Dhugald/OP_ROVER/Photos/IMG_0927.JPG

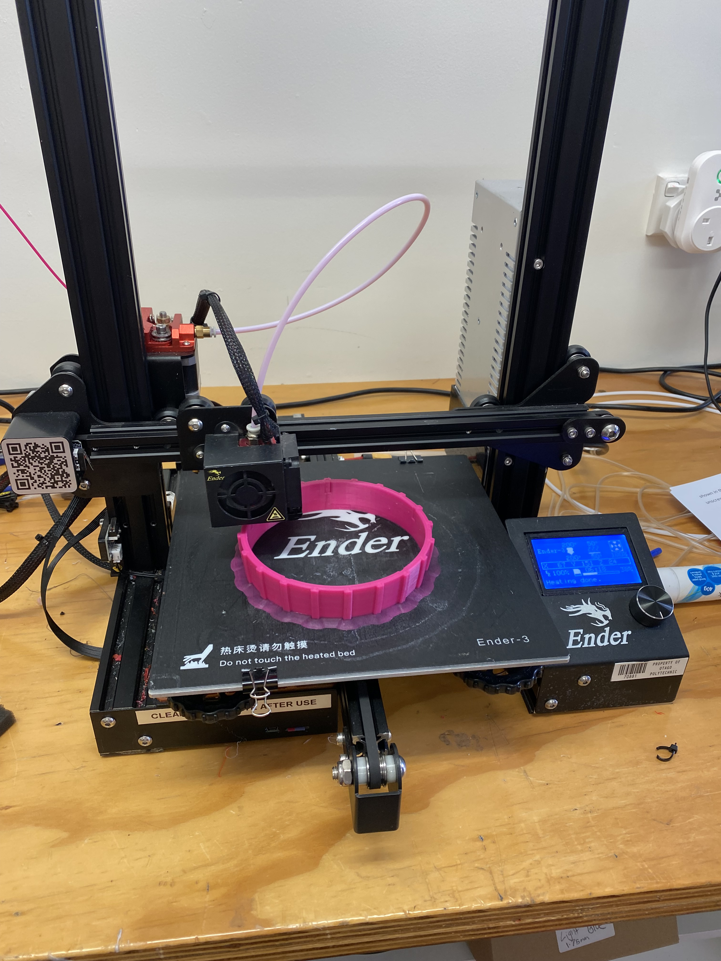
Photos/IMG_0927.JPG
