Dhugald/OP_ROVER/Photos/IMG_0928.JPG

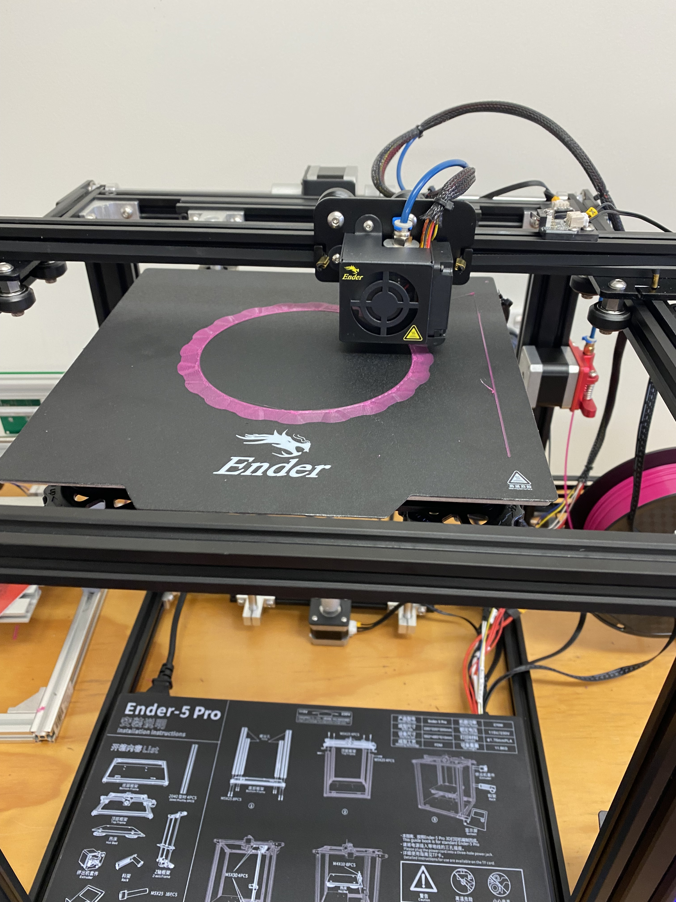
Photos/IMG_0928.JPG
