Dhugald/OP_ROVER/Photos/IMG_0930.JPG

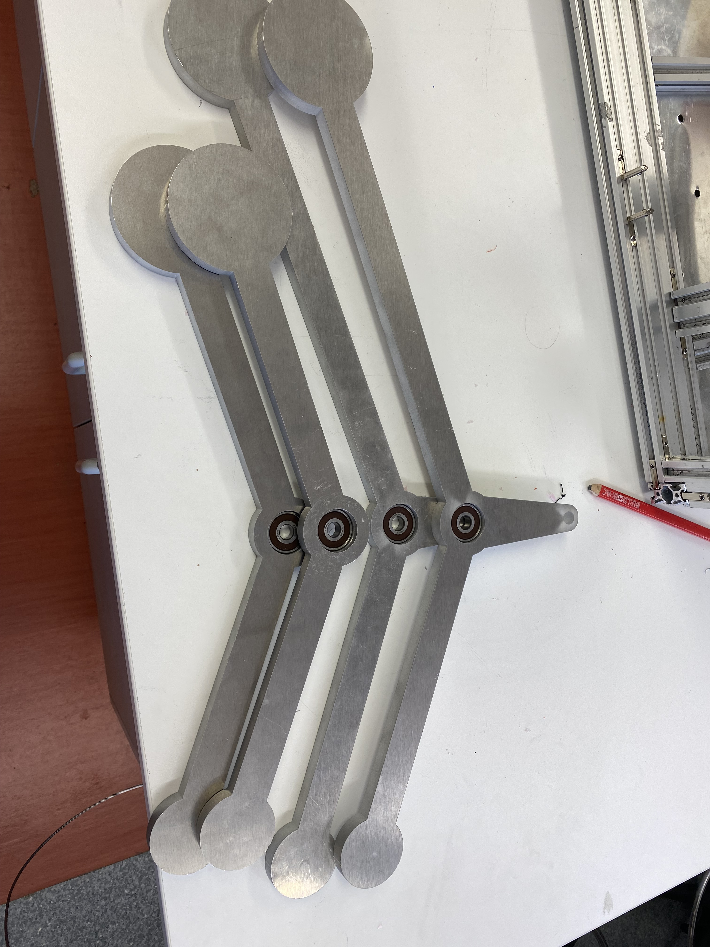
Photos/IMG_0930.JPG
