Dhugald/OP_ROVER/Photos/IMG_0931.JPG

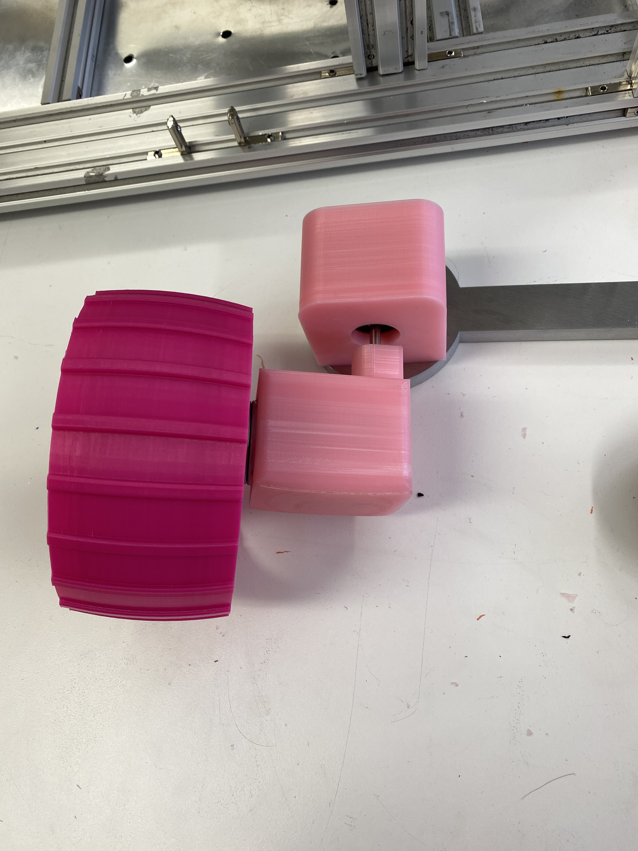
Photos/IMG_0931.JPG
