Dhugald/OP_ROVER/Photos/IMG_0986.JPG

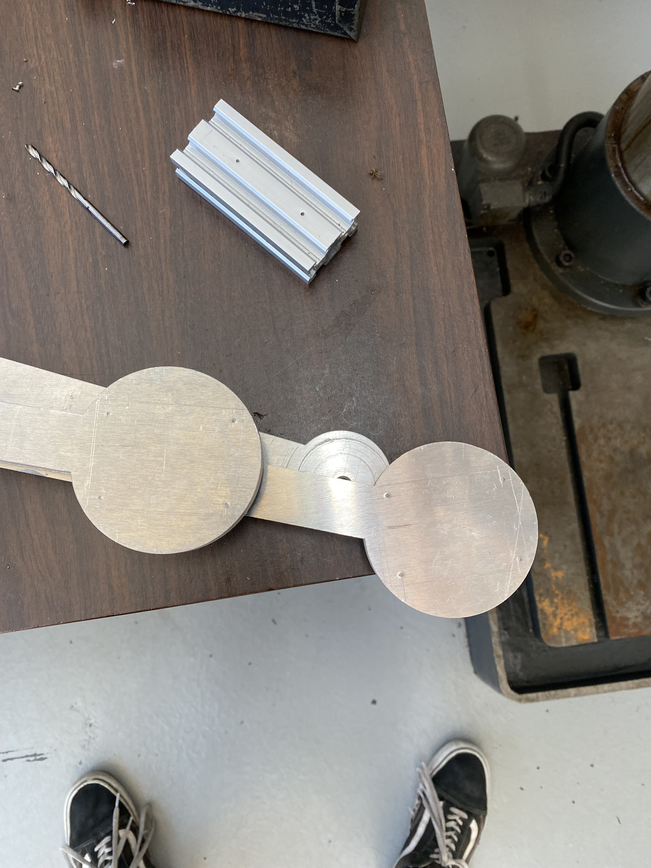
Photos/IMG_0986.JPG
