Dhugald/OP_ROVER/Photos/IMG_0987.JPG

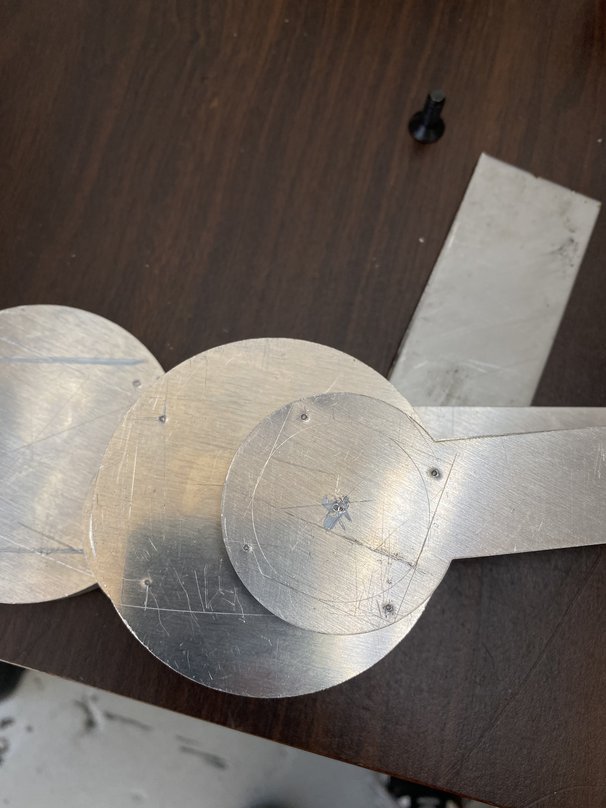
Photos/IMG_0987.JPG
