Dhugald/OP_ROVER/3D parts/Lidar Scanner Brackets/LIDAR-Mount-Pocket.stl

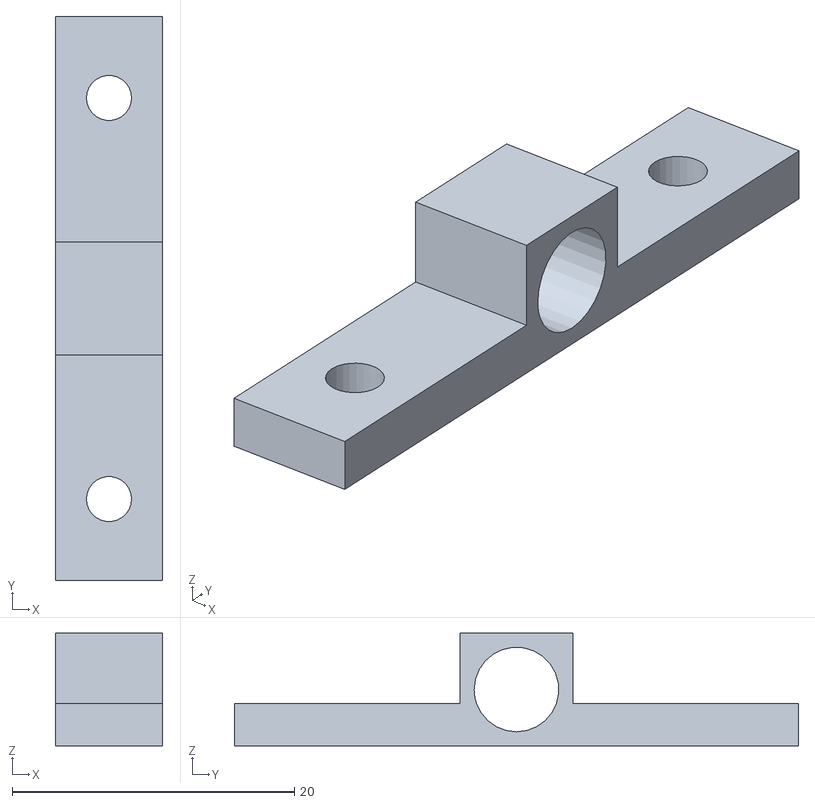
[picture p29: CAD file, 2021-09-20]
3D parts/Lidar Scanner Brackets/LIDAR-Mount-Pocket.stl
7.62 x 40.0 x 8.00
