Dhugald/OP_ROVER/3D parts/Rover Bogie Rocker v7.stl

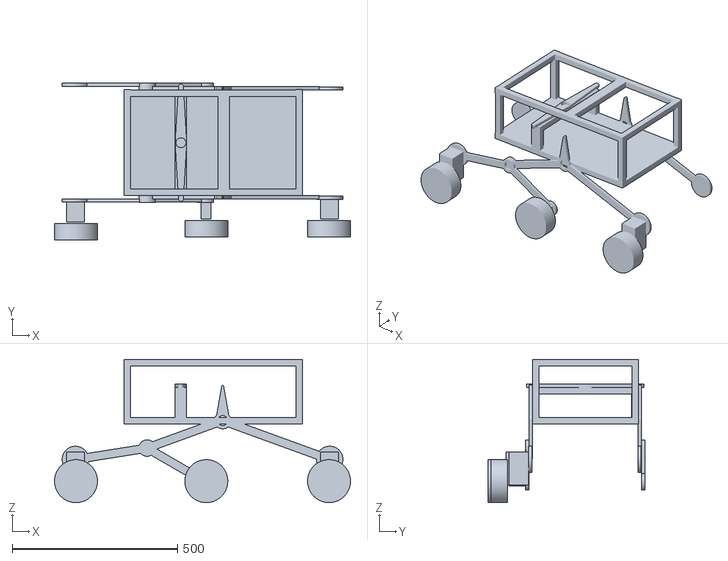
[picture p30: CAD file, 2021-09-16]
3D parts/Rover Bogie Rocker v7.stl
894.9 x 473.6 x 433.2
