Dhugald/OP_ROVER/3D parts/Lidar Scanner Brackets/LIDAR-Sensor-Chamfer001.stl

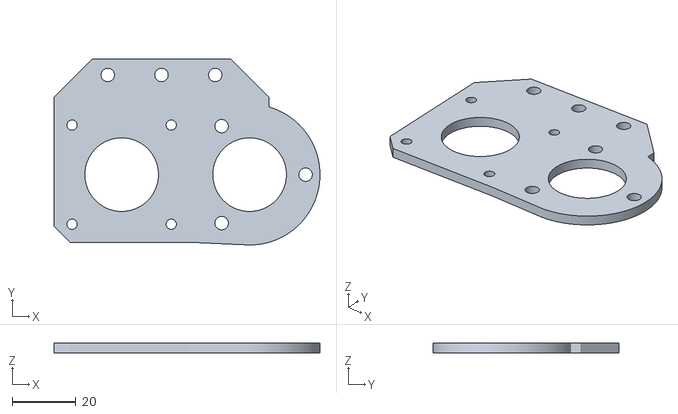
[picture p31: CAD file, 2021-09-20]
3D parts/Lidar Scanner Brackets/LIDAR-Sensor-Chamfer001.stl
83.1 x 58.2 x 3.00
