Dhugald/OP_ROVER/3D parts/Stepper_Holder v3.stl

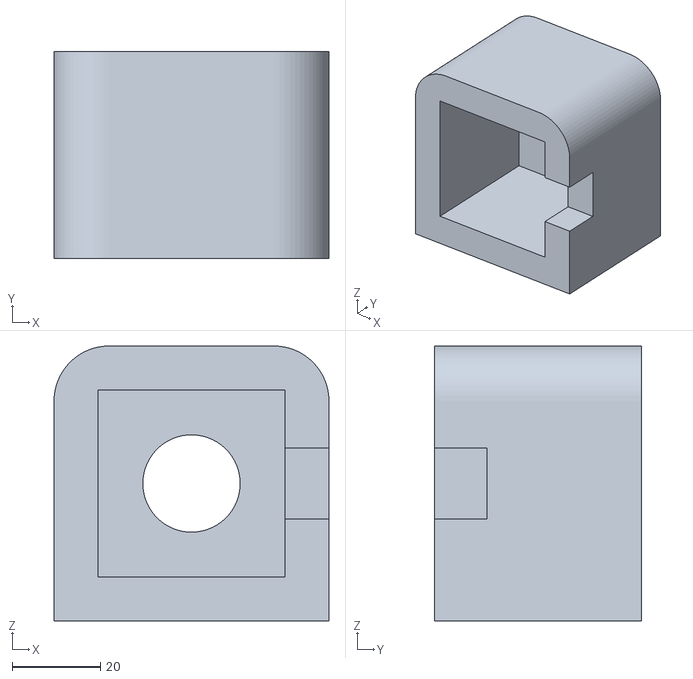
[picture p32: CAD file, 2021-08-12]
3D parts/Stepper_Holder v3.stl
62.5 x 47.1 x 62.5
