Dhugald/OP_ROVER/3D parts/Rover_Ankle Joint v2.stl

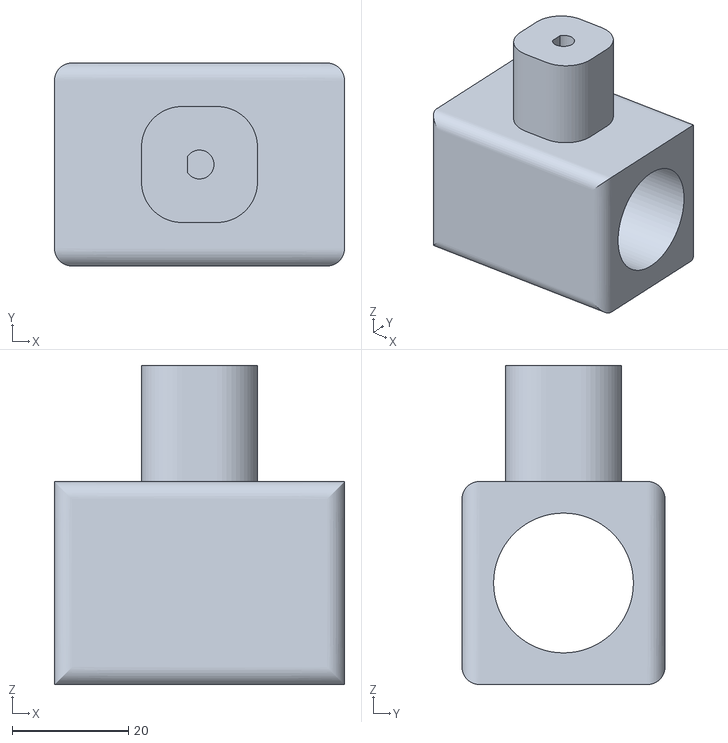
[picture p33: CAD file, 2021-08-09]
3D parts/Rover_Ankle Joint v2.stl
50.0 x 35.0 x 55.0
